umairahmadh/innavsys/Hardware/Robot_design/top view.png

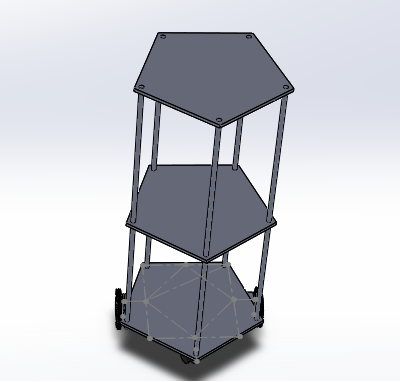
Hardware/Robot_design/top view.png
