umairahmadh/innavsys/Hardware/Robot_design/weight/rod and tube.png

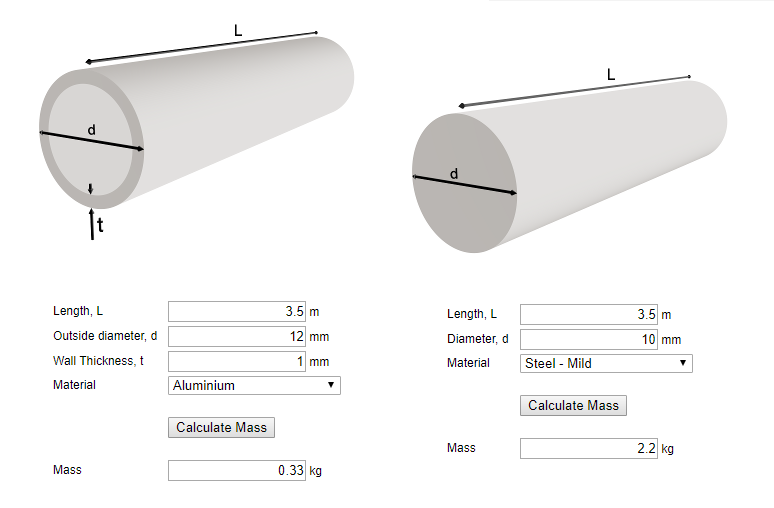
Hardware/Robot_design/weight/rod and tube.png
