umairahmadh/innavsys/Presentations/final_bot_1.png

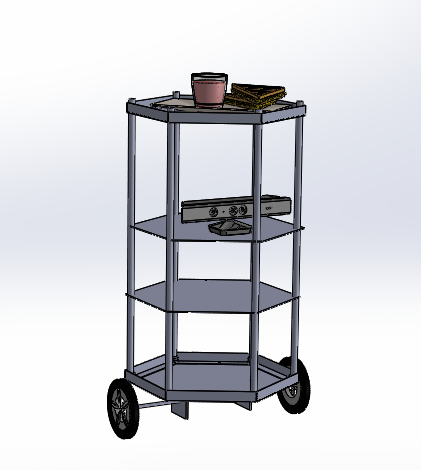
Presentations/final_bot_1.png
