umairahmadh/innavsys/Publications/images/Guyson-Robot-on-Rail-Blast-Systems.jpg

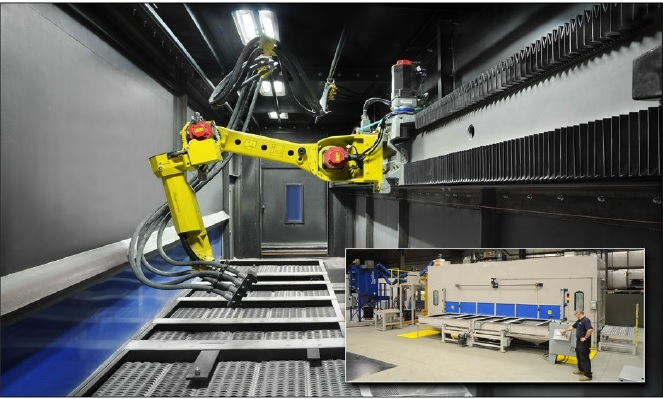
Publications/images/Guyson-Robot-on-Rail-Blast-Systems.jpg
