umairahmadh/innavsys/Publications/images/robots_blogpost_estimote_150ppi-03.png

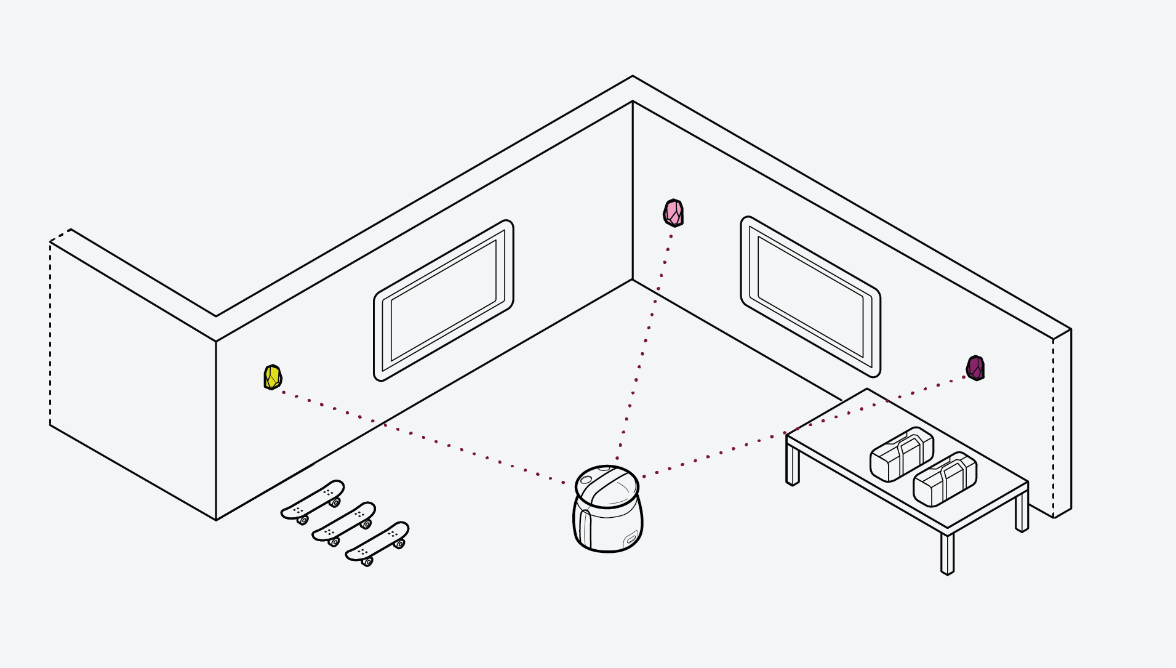
Publications/images/robots_blogpost_estimote_150ppi-03.png
