umairahmadh/innavsys/Hardware/Robot_design/kinect-1.snapshot.2/lower part.SLDPRT

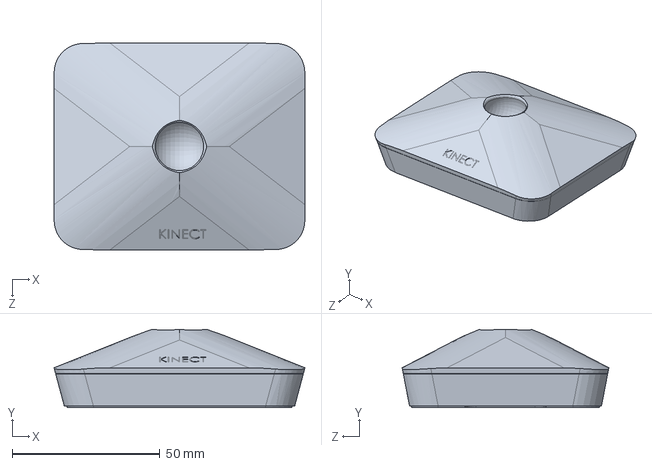
[picture p126: CAD file, 2020-02-25]
Hardware/Robot_design/kinect-1.snapshot.2/lower part.SLDPRT
85.0 x 26.5 x 70.0 mm
