umairahmadh/innavsys/Hardware/Robot_design/wheel/Renderings/roue.STEP

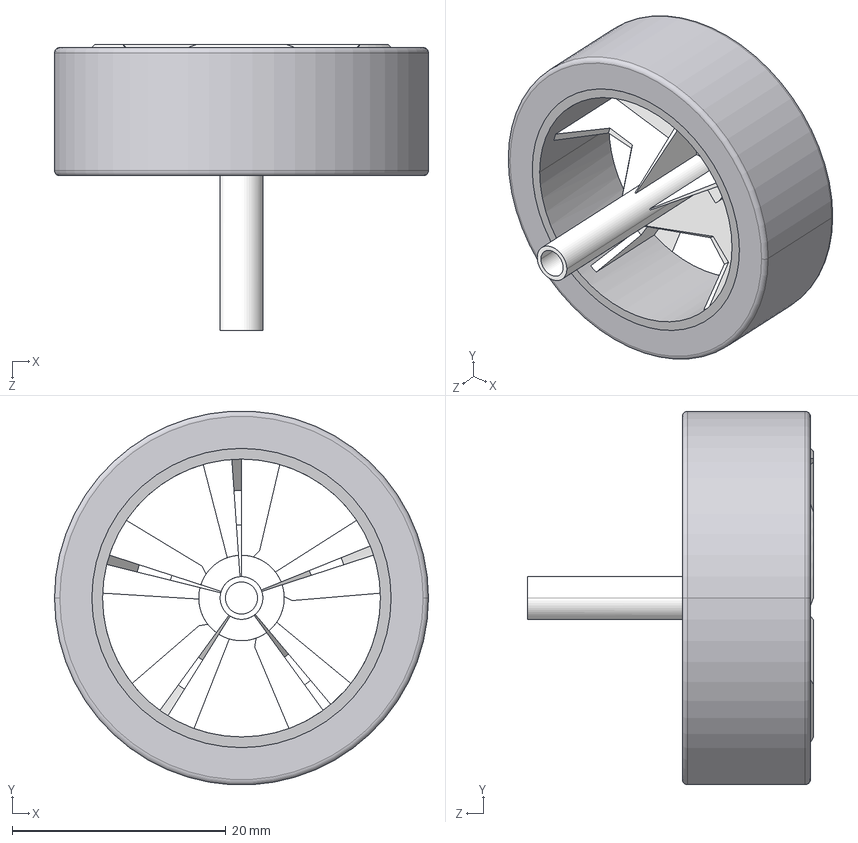
[picture p127: CAD file, 2020-02-25]
Hardware/Robot_design/wheel/Renderings/roue.STEP
35.0 x 34.9 x 26.8 mm
tire
disque roue
