umairahmadh/innavsys/Hardware/Robot_design/wheel_shaft.SLDPRT

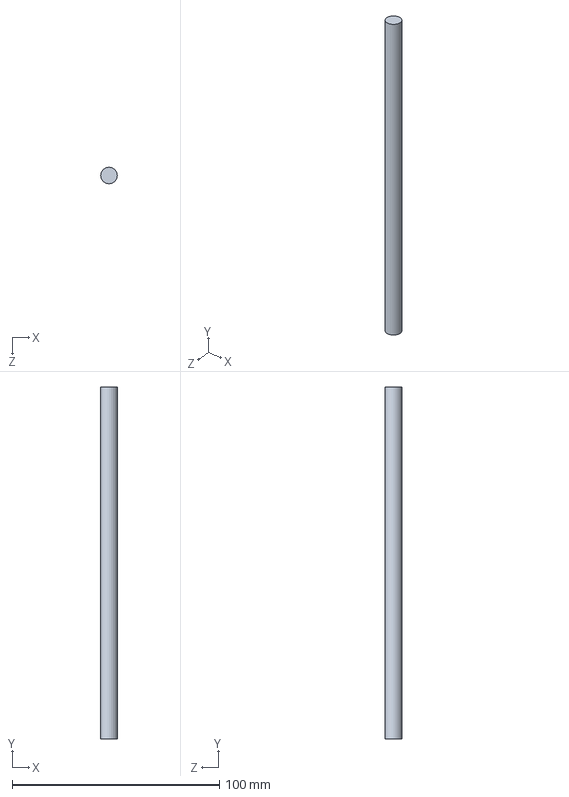
[picture p128: CAD file, 2020-02-25]
Hardware/Robot_design/wheel_shaft.SLDPRT
8.00 x 170.0 x 8.00 mm
