umairahmadh/innavsys/Hardware/Robot_design/bottom/hex-plate.SLDPRT

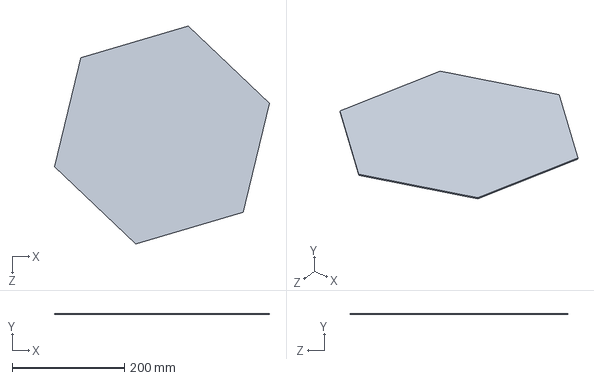
[picture p129: CAD file, 2020-02-25]
Hardware/Robot_design/bottom/hex-plate.SLDPRT
383.6 x 2.00 x 388.8 mm
