umairahmadh/innavsys/Hardware/Robot_design/grilled-cheese-plate-1.snapshot.2/Gaspatxo.SLDPRT

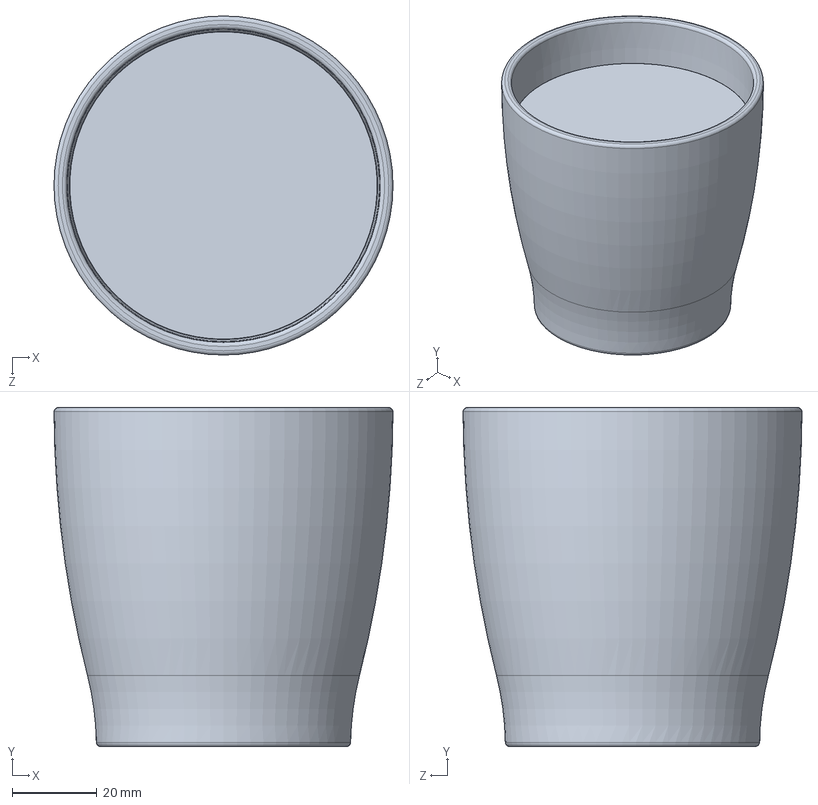
[picture p130: CAD file, 2020-02-25]
Hardware/Robot_design/grilled-cheese-plate-1.snapshot.2/Gaspatxo.SLDPRT
80.0 x 80.0 x 80.0 mm
