umairahmadh/innavsys/Hardware/Robot_design/Part2.SLDPRT

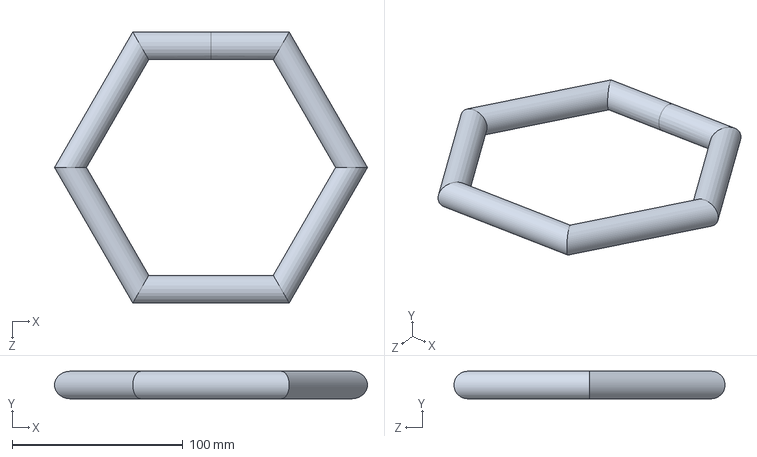
[picture p131: CAD file, 2020-02-25]
Hardware/Robot_design/Part2.SLDPRT
183.1 x 16.2 x 158.6 mm
