umairahmadh/innavsys/Hardware/Robot_design/wheel/Renderings/tire.SLDPRT

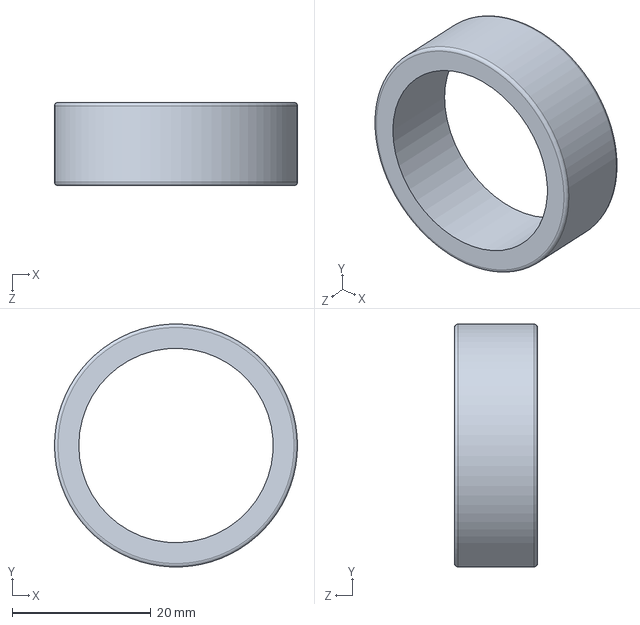
[picture p132: CAD file, 2020-02-25]
Hardware/Robot_design/wheel/Renderings/tire.SLDPRT
35.0 x 35.0 x 12.0 mm
