umairahmadh/innavsys/Hardware/Robot_design/bottom/Glasses 3 (1).SLDPRT

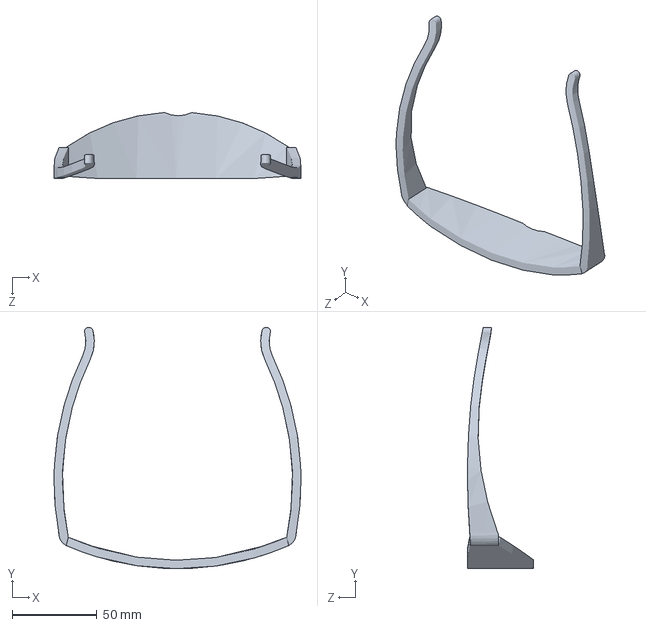
[picture p133: CAD file, 2020-02-25]
Hardware/Robot_design/bottom/Glasses 3 (1).SLDPRT
145.6 x 142.3 x 38.9 mm
