umairahmadh/innavsys/Hardware/Robot_design/disque roue.SLDPRT

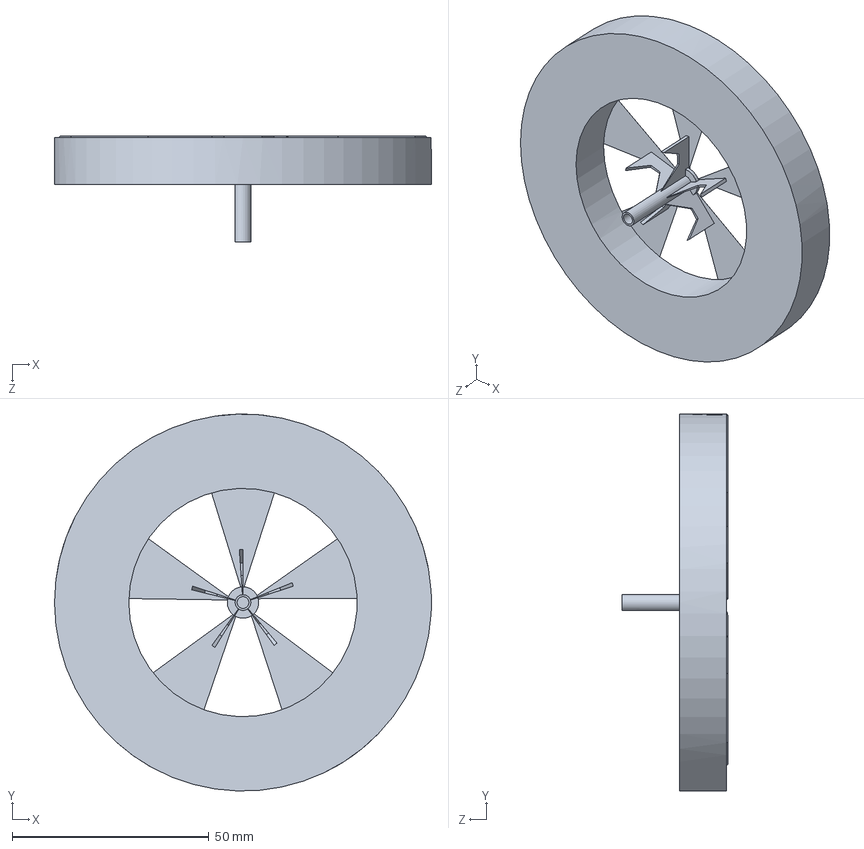
[picture p134: CAD file, 2020-02-25]
Hardware/Robot_design/disque roue.SLDPRT
95.8 x 95.7 x 26.8 mm
