umairahmadh/innavsys/Hardware/Robot_design/2 inch caster wheel.SLDPRT

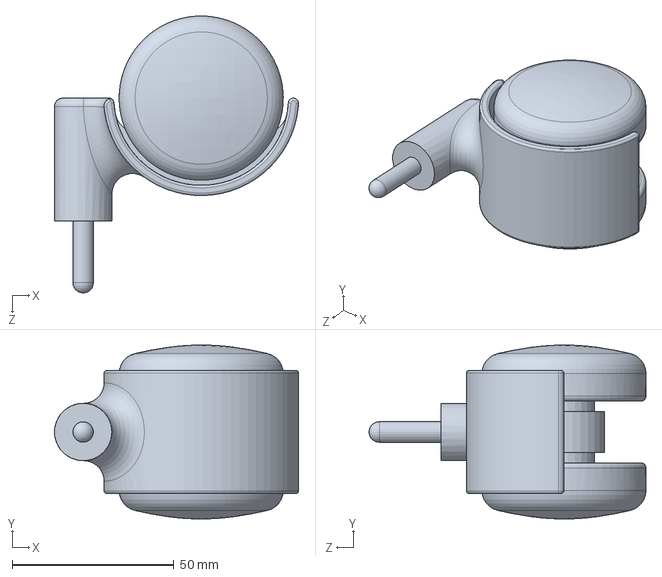
[picture p135: CAD file, 2020-02-25]
Hardware/Robot_design/2 inch caster wheel.SLDPRT
75.5 x 53.8 x 85.7 mm
