umairahmadh/innavsys/Hardware/Robot_design/tire.SLDPRT

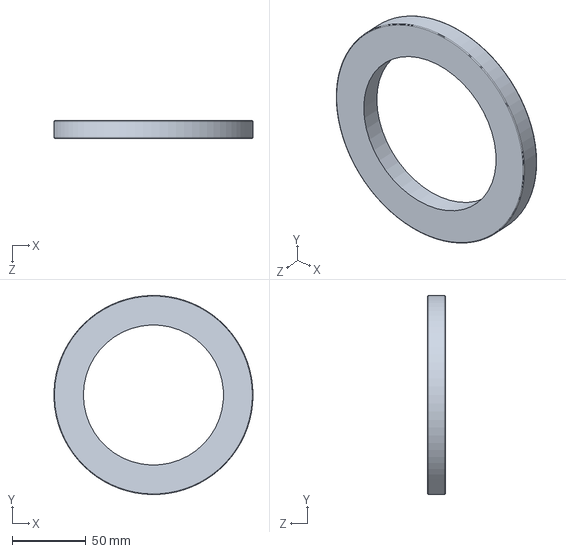
[picture p136: CAD file, 2020-02-25]
Hardware/Robot_design/tire.SLDPRT
134.9 x 135.0 x 12.0 mm
