umairahmadh/innavsys/Hardware/Robot_design/Part1.SLDPRT

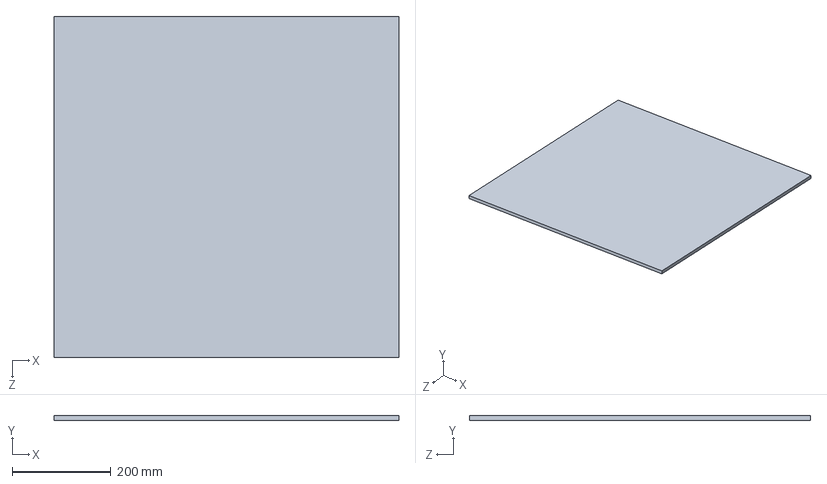
[picture p137: CAD file, 2020-02-25]
Hardware/Robot_design/Part1.SLDPRT
700.0 x 10.0 x 692.8 mm
