umairahmadh/innavsys/Hardware/Robot_design/threadrod.SLDPRT

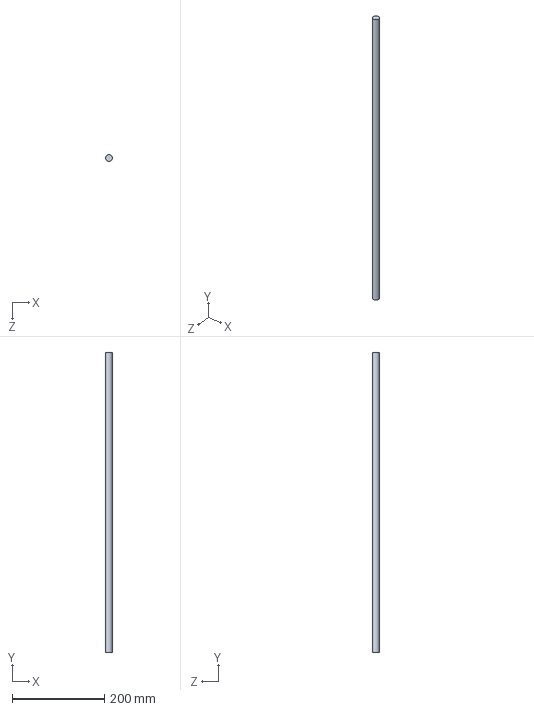
[picture p138: CAD file, 2020-02-25]
Hardware/Robot_design/threadrod.SLDPRT
15.0 x 650.0 x 15.0 mm
