umairahmadh/innavsys/Hardware/Robot_design/kinect_stand.SLDPRT

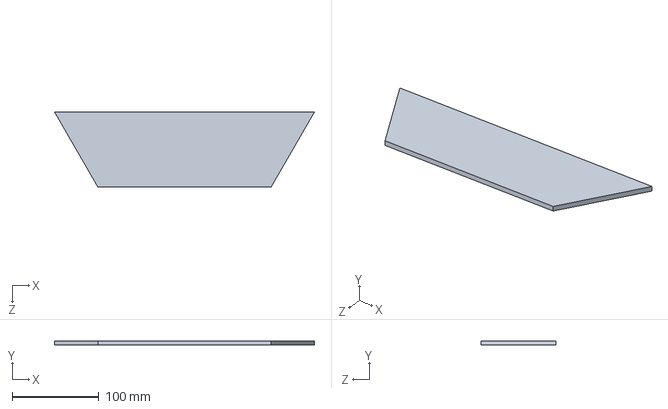
[picture p139: CAD file, 2020-02-25]
Hardware/Robot_design/kinect_stand.SLDPRT
300.0 x 5.00 x 86.6 mm
