umairahmadh/innavsys/Hardware/Robot_design/robotstackplate.SLDPRT

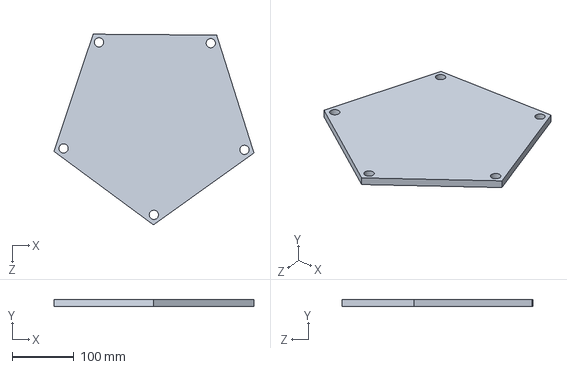
[picture p140: CAD file, 2020-02-25]
Hardware/Robot_design/robotstackplate.SLDPRT
323.6 x 11.0 x 308.5 mm
